DavidGR777/Feed-Tech-Solution/docs/High level schemes/Arquitectura.jpg

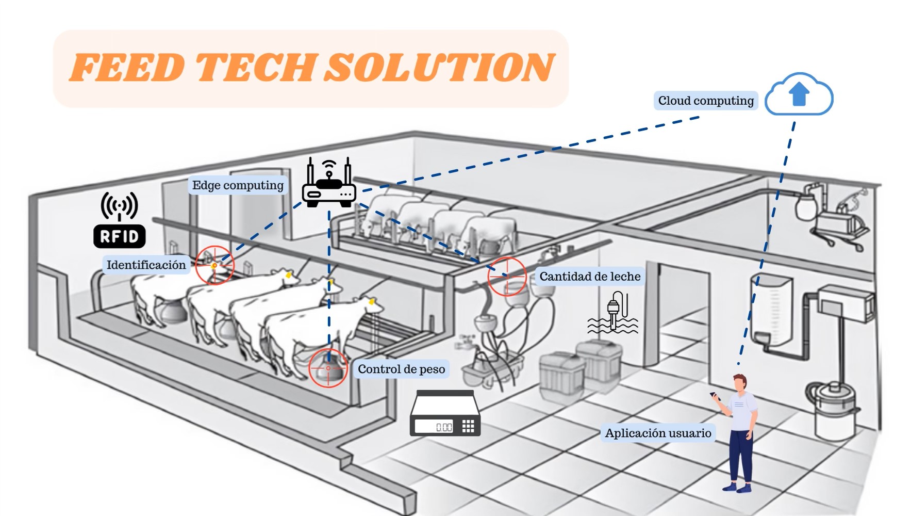
docs/High level schemes/Arquitectura.jpg
