DavidGR777/Feed-Tech-Solution/docs/High level schemes/Diagrama de bloques.png

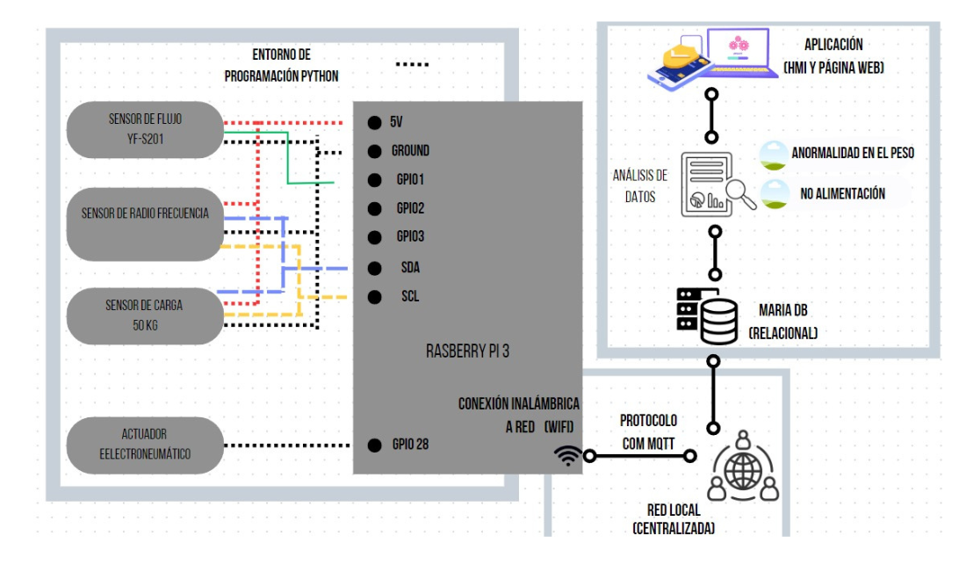
docs/High level schemes/Diagrama de bloques.png
