DavidGR777/Feed-Tech-Solution/docs/images/Folletos.jpg

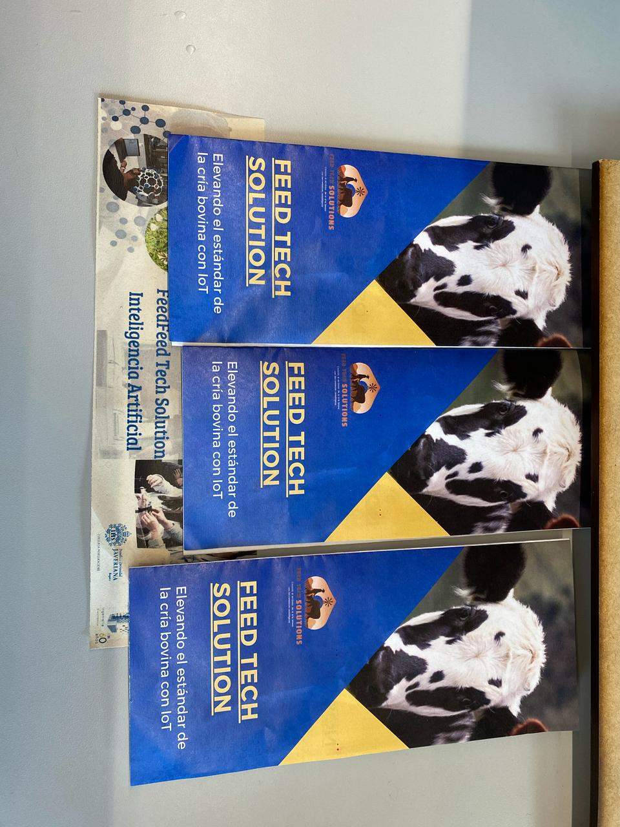
docs/images/Folletos.jpg
