DavidGR777/Feed-Tech-Solution/docs/images/Implementacion 1.jpg

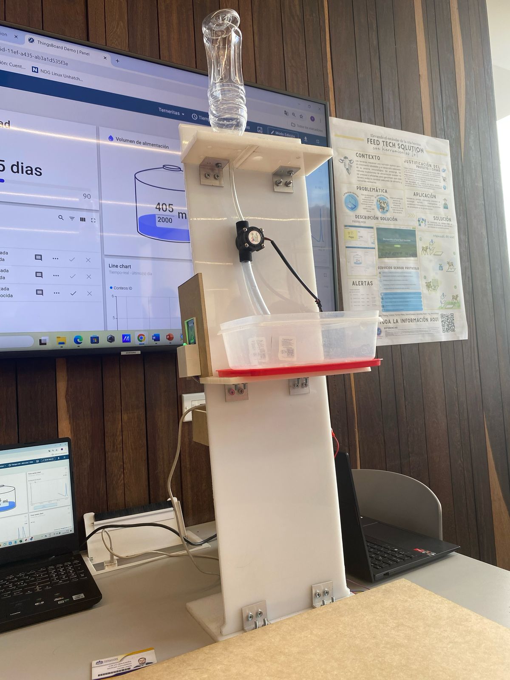
docs/images/Implementacion 1.jpg
