DavidGR777/Feed-Tech-Solution/docs/images/Implementacion 2.jpg

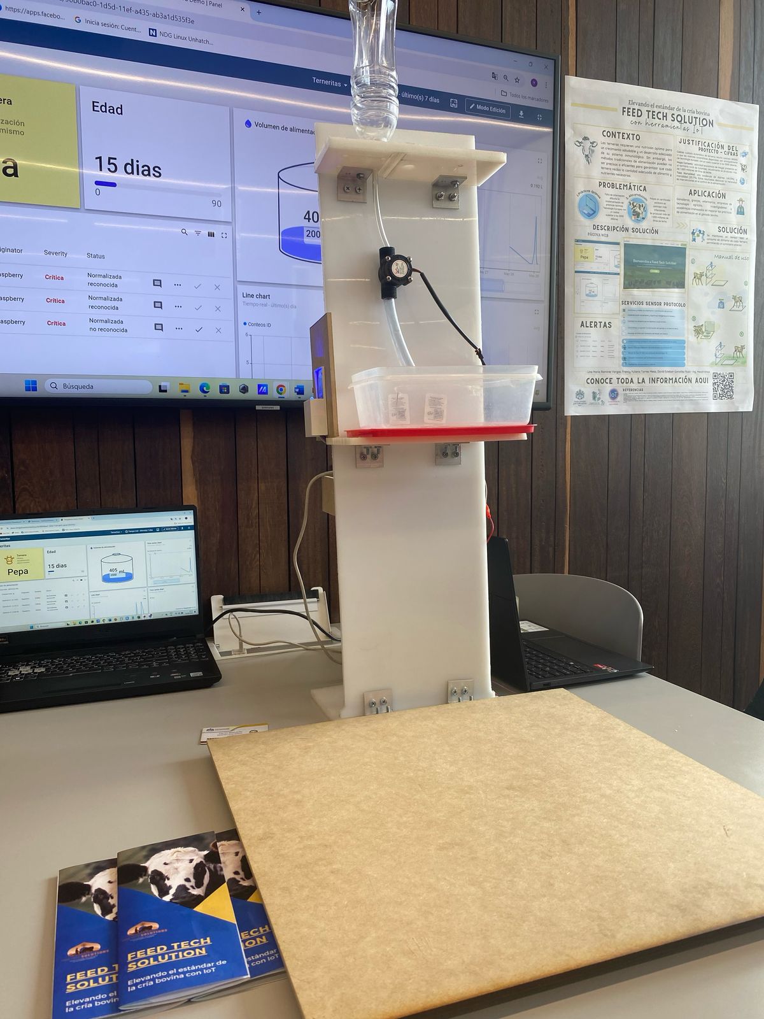
docs/images/Implementacion 2.jpg
