DavidGR777/Feed-Tech-Solution/web-page/img/__page-0001.jpg

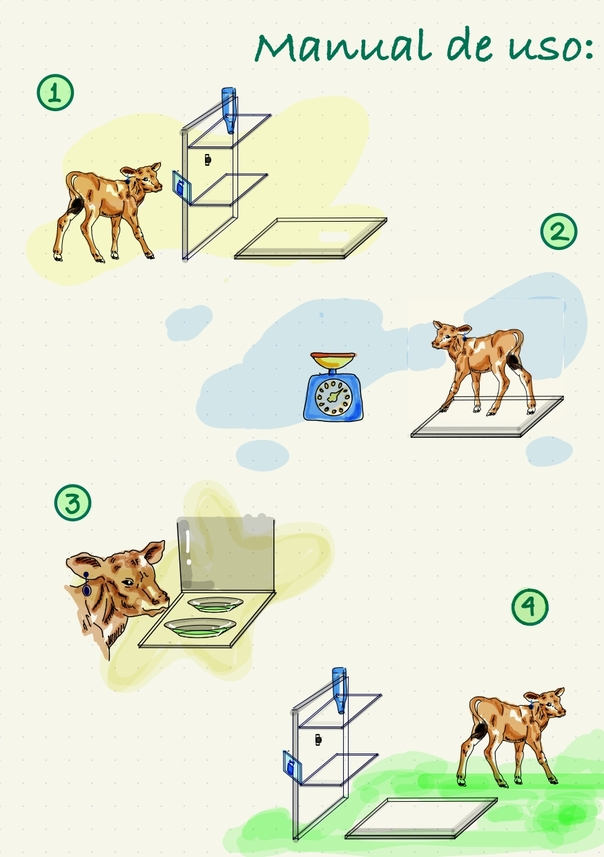
web-page/img/__page-0001.jpg
