DavidGR777/Feed-Tech-Solution/web-page/img/footer.jpg

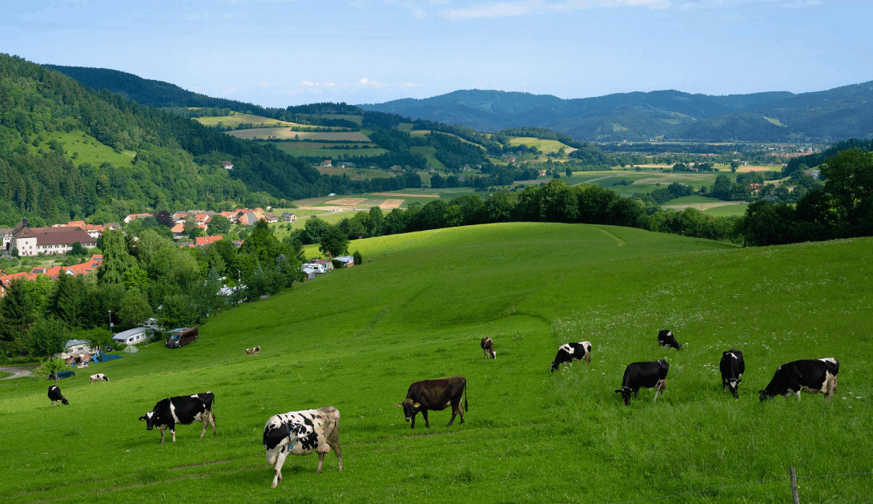
web-page/img/footer.jpg
