DavidGR777/Feed-Tech-Solution/web-page/img/header.jpg

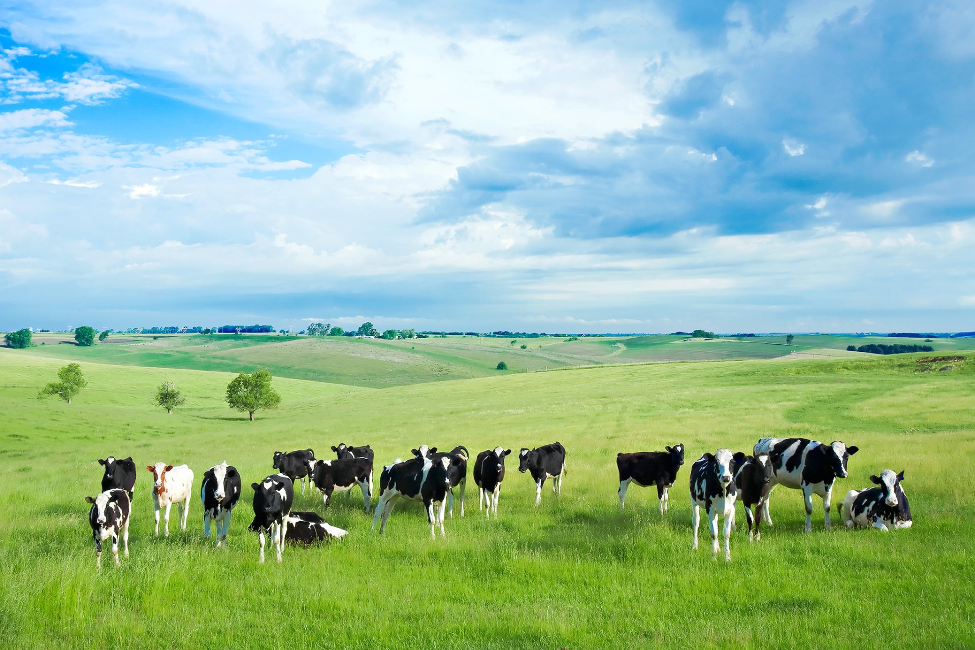
web-page/img/header.jpg
