DavidGR777/Feed-Tech-Solution/web-page/img/imagen1.png

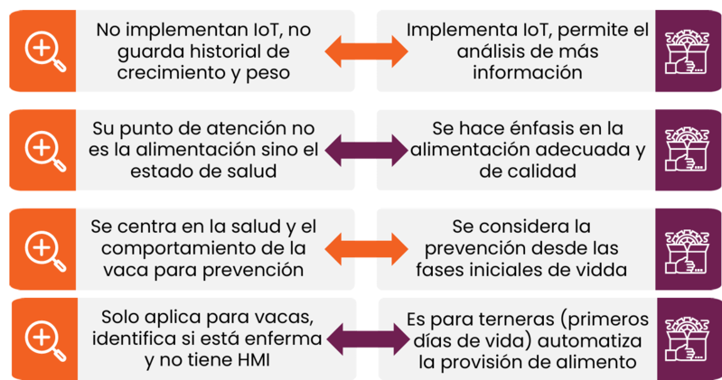
web-page/img/imagen1.png
