DavidGR777/Feed-Tech-Solution/web-page/img/imagen2.png

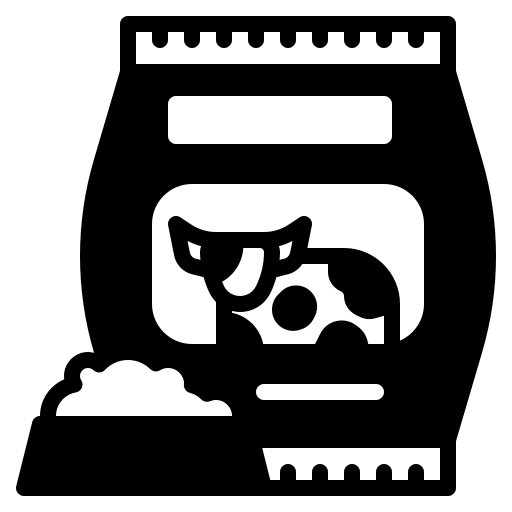
web-page/img/imagen2.png
