DavidGR777/Feed-Tech-Solution/web-page/img/imagen5.jpg

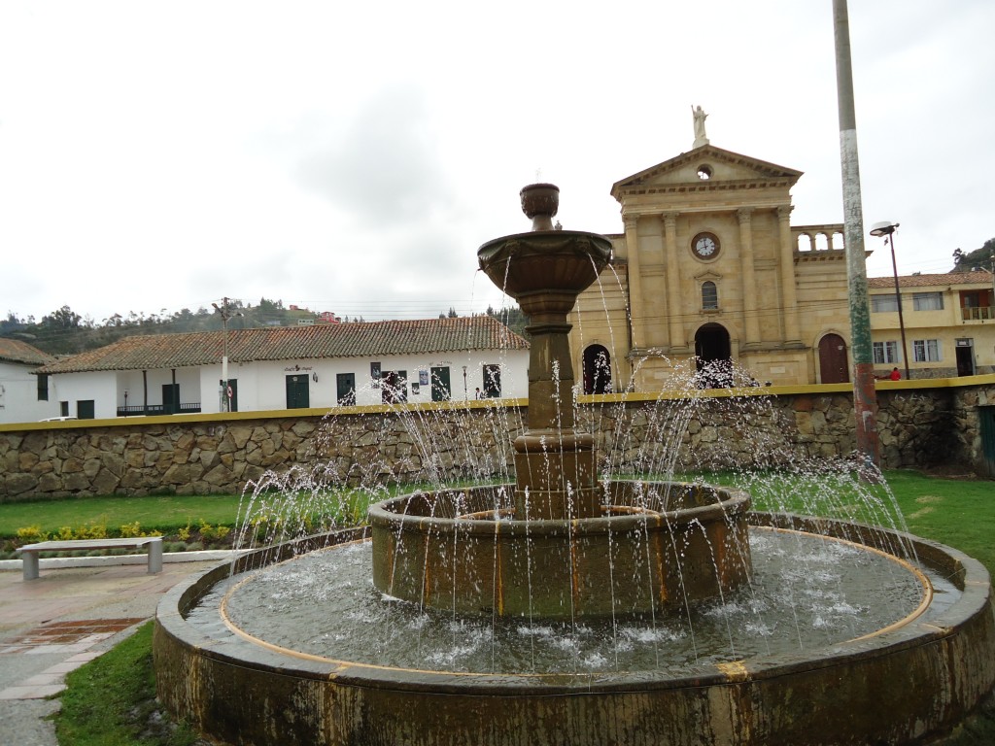
web-page/img/imagen5.jpg
