DavidGR777/Feed-Tech-Solution/web-page/img/imagen6.jpeg

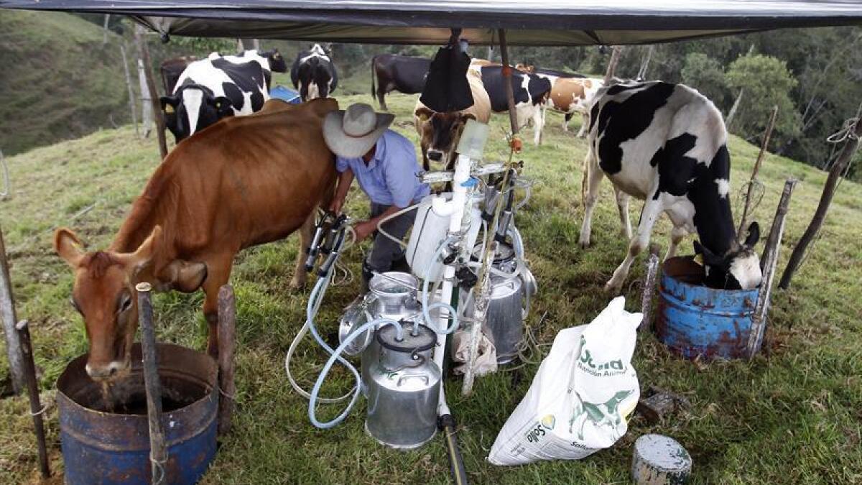
web-page/img/imagen6.jpeg
