DavidGR777/Feed-Tech-Solution/web-page/img/imagen7.jpg

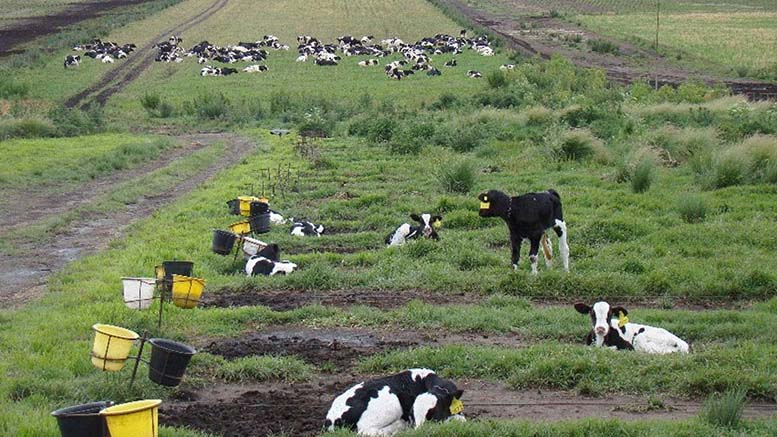
web-page/img/imagen7.jpg
