DavidGR777/Feed-Tech-Solution/web-page/img/imagen8.jpg

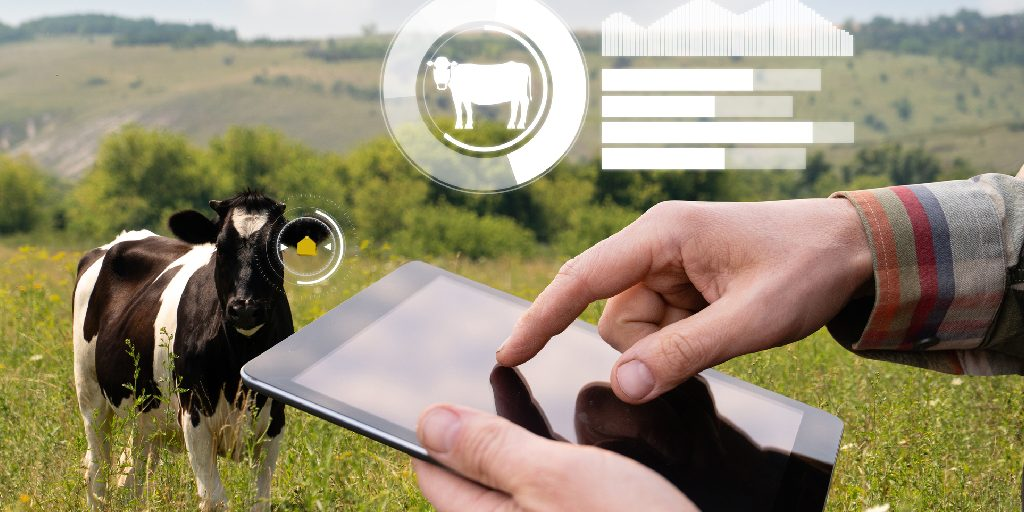
web-page/img/imagen8.jpg
