DavidGR777/Feed-Tech-Solution/web-page/img/imagen10.png

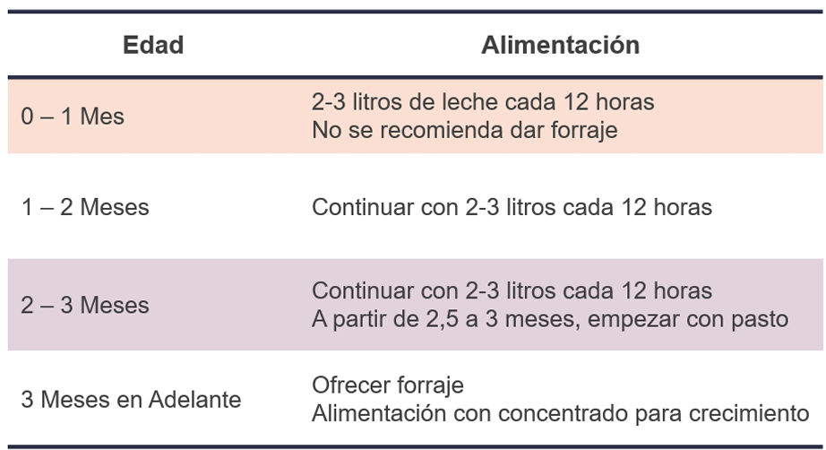
web-page/img/imagen10.png
