DavidGR777/Feed-Tech-Solution/web-page/img/imagen14.png

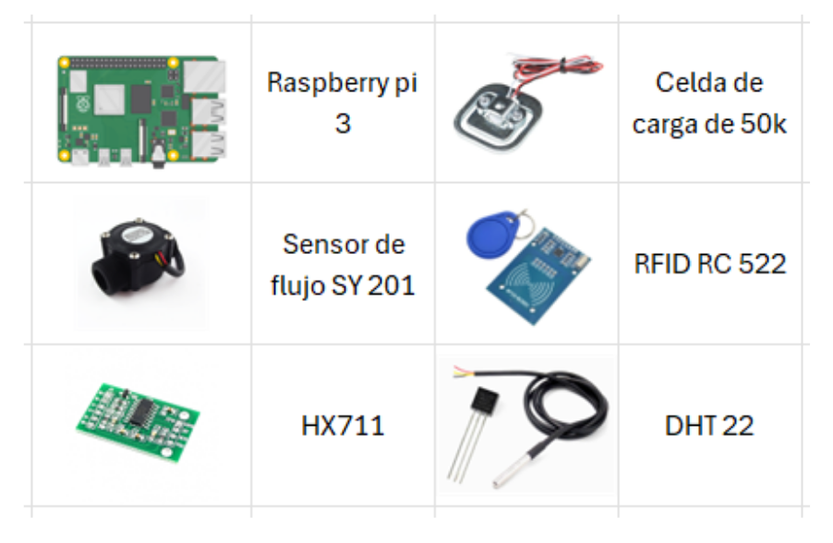
web-page/img/imagen14.png
