DavidGR777/Feed-Tech-Solution/web-page/img/imagen15.jpg

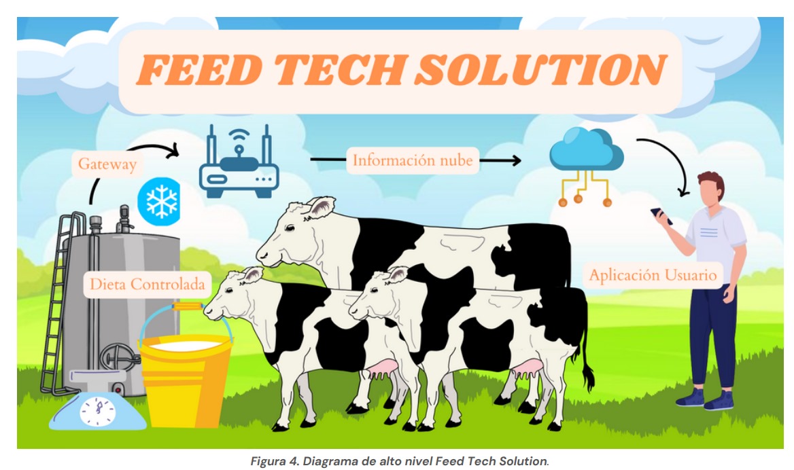
web-page/img/imagen15.jpg
