DavidGR777/Feed-Tech-Solution/web-page/img/imagen16.png

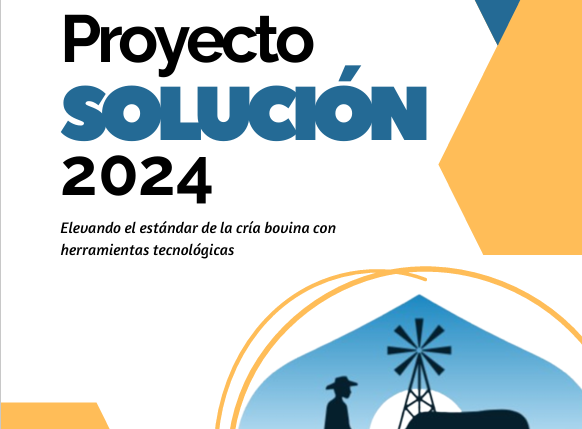
web-page/img/imagen16.png
