DavidGR777/Feed-Tech-Solution/web-page/img/img-2.jpg

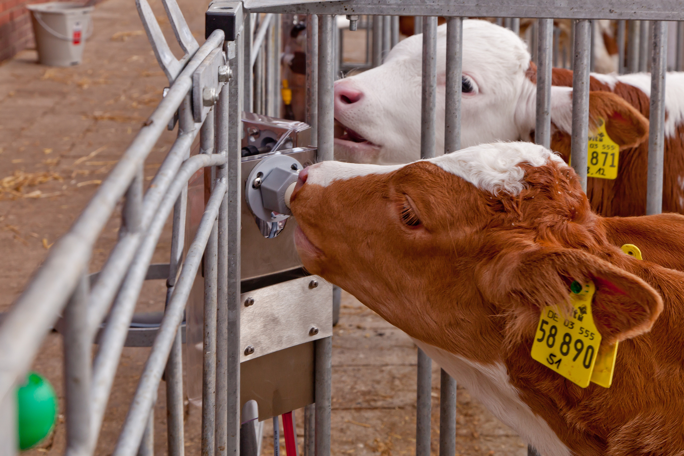
web-page/img/img-2.jpg
