DavidGR777/Feed-Tech-Solution/web-page/img/img-9.jpg

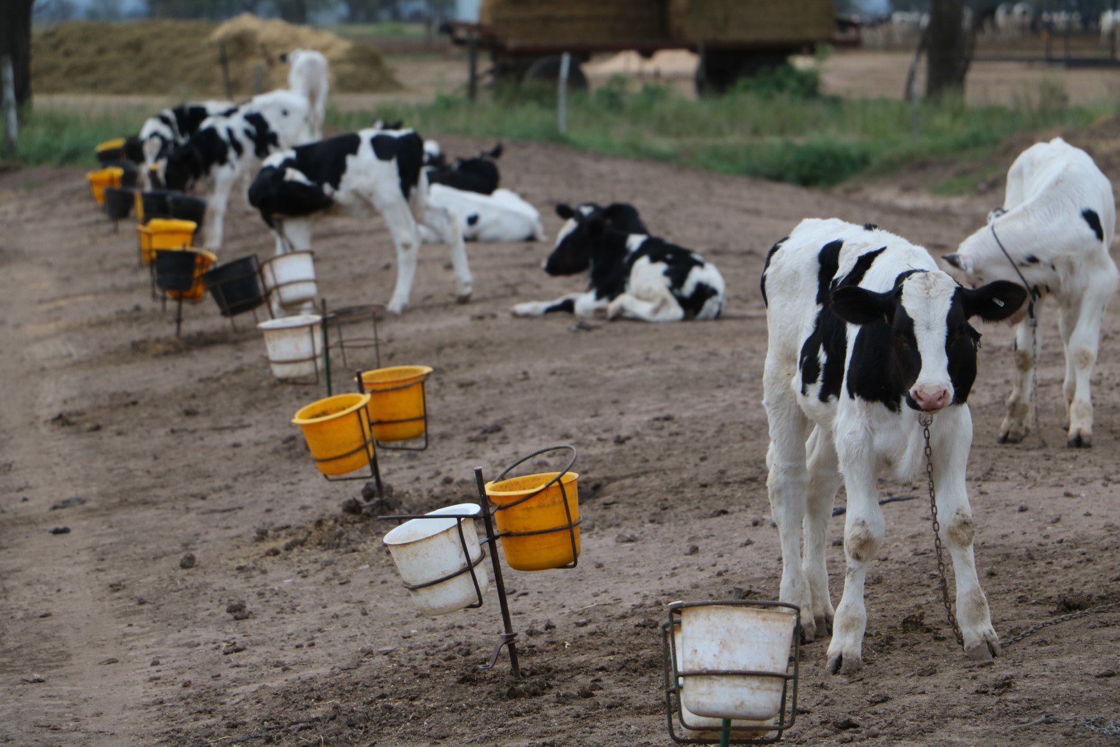
web-page/img/img-9.jpg
