DavidGR777/Feed-Tech-Solution/web-page/img/img-17.jpg

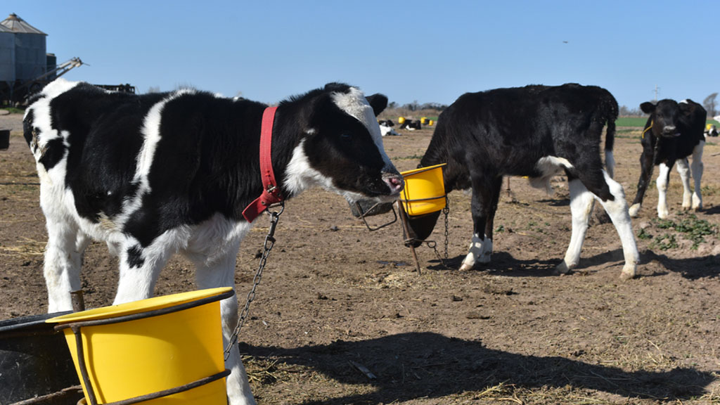
web-page/img/img-17.jpg
