DavidGR777/Feed-Tech-Solution/cad-design/Celda de carga/SIDE RIVET, 50 kg Load Cell Resistance Strain Half Bridge Sensor.SLDPRT

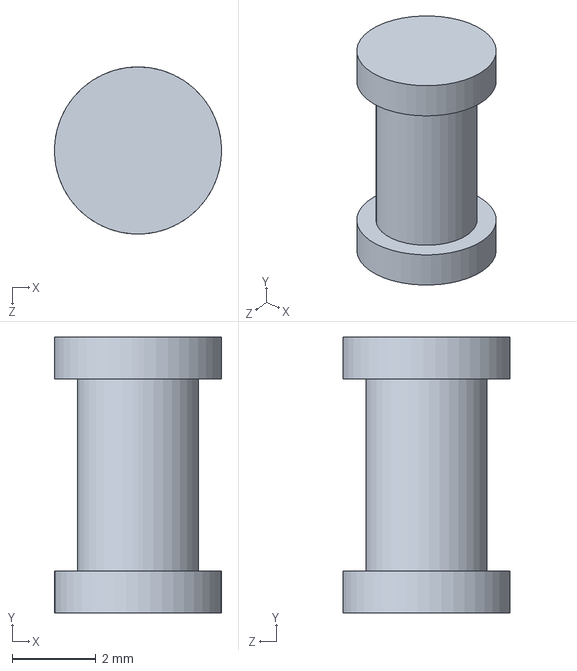
[picture p64: CAD file, 2025-03-24]
cad-design/Celda de carga/SIDE RIVET, 50 kg Load Cell Resistance Strain Half Bridge Sensor.SLDPRT
4.00 x 6.60 x 4.00 mm
