DavidGR777/Feed-Tech-Solution/cad-design/LCD/metal_casing.SLDPRT

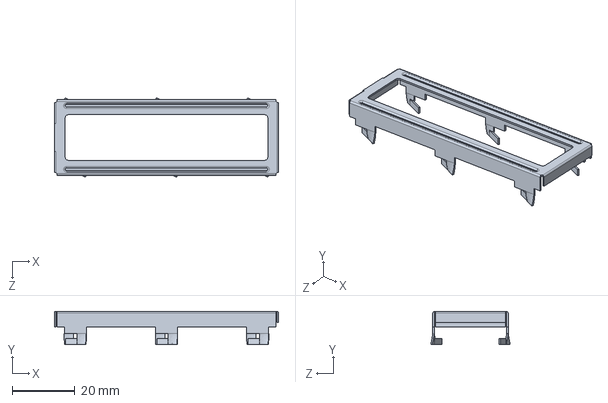
[picture p65: CAD file, 2025-03-24]
cad-design/LCD/metal_casing.SLDPRT
71.2 x 10.6 x 25.3 mm
