DavidGR777/Feed-Tech-Solution/cad-design/Soporte RFID.SLDPRT

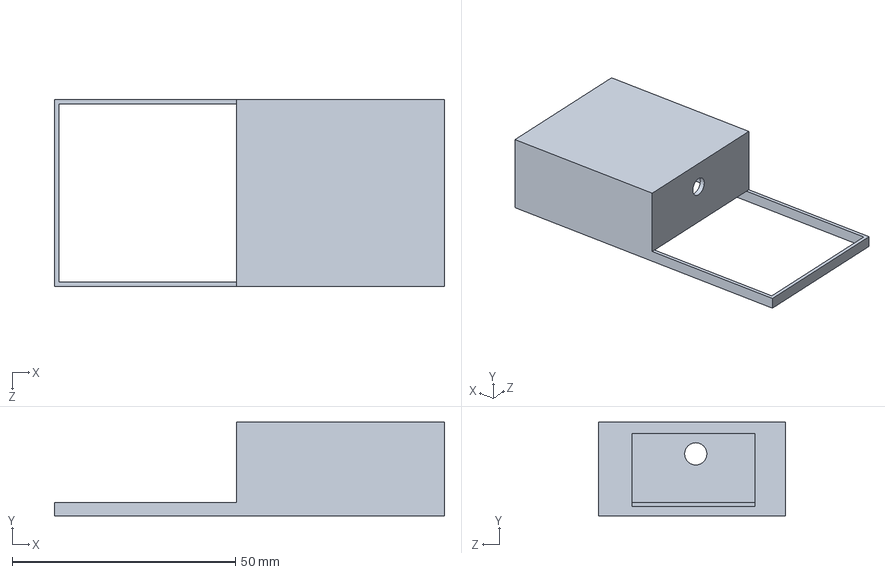
[picture p66: CAD file, 2025-03-24]
cad-design/Soporte RFID.SLDPRT
87.3 x 21.0 x 41.9 mm
