DavidGR777/Feed-Tech-Solution/cad-design/Celda de carga/WIRED CONNECTION, 50 kg Load Cell Resistance Strain Half Bridge Sensor.SLDPRT

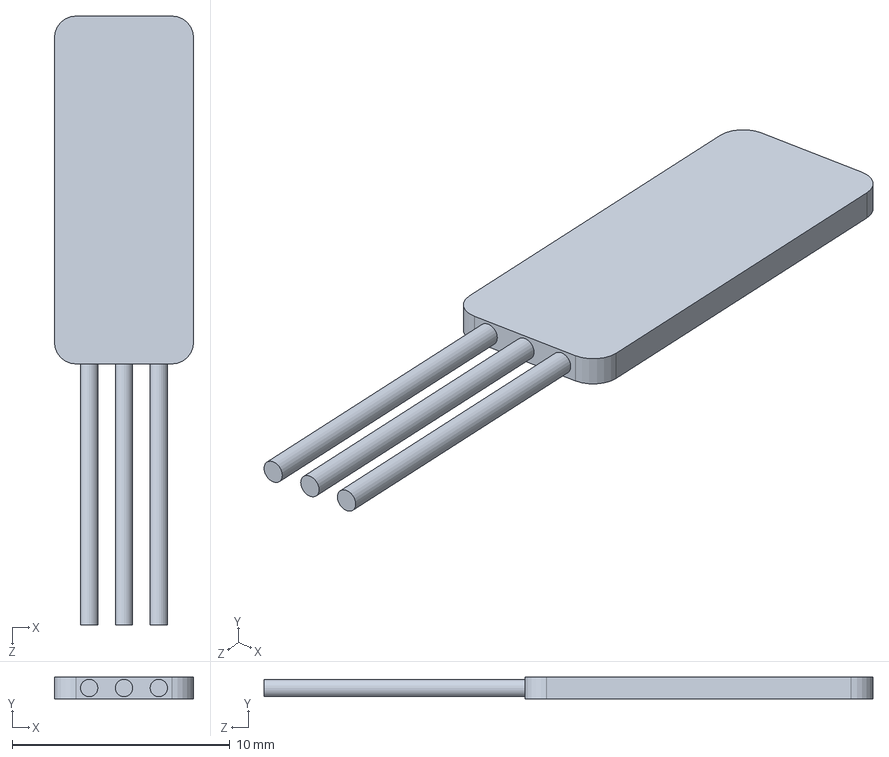
[picture p67: CAD file, 2025-03-24]
cad-design/Celda de carga/WIRED CONNECTION, 50 kg Load Cell Resistance Strain Half Bridge Sensor.SLDPRT
6.40 x 1.00 x 28.0 mm
