DavidGR777/Feed-Tech-Solution/cad-design/LCD/conductors.SLDPRT

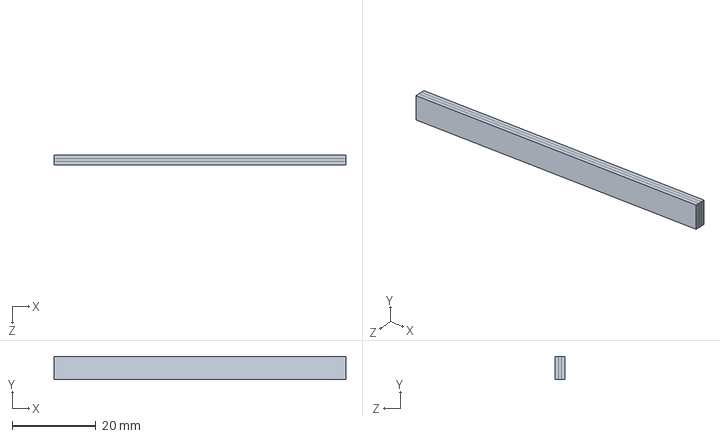
[picture p68: CAD file, 2025-03-24]
cad-design/LCD/conductors.SLDPRT
69.7 x 5.50 x 2.50 mm
