DavidGR777/Feed-Tech-Solution/cad-design/RFID-RC522 simple.SLDPRT

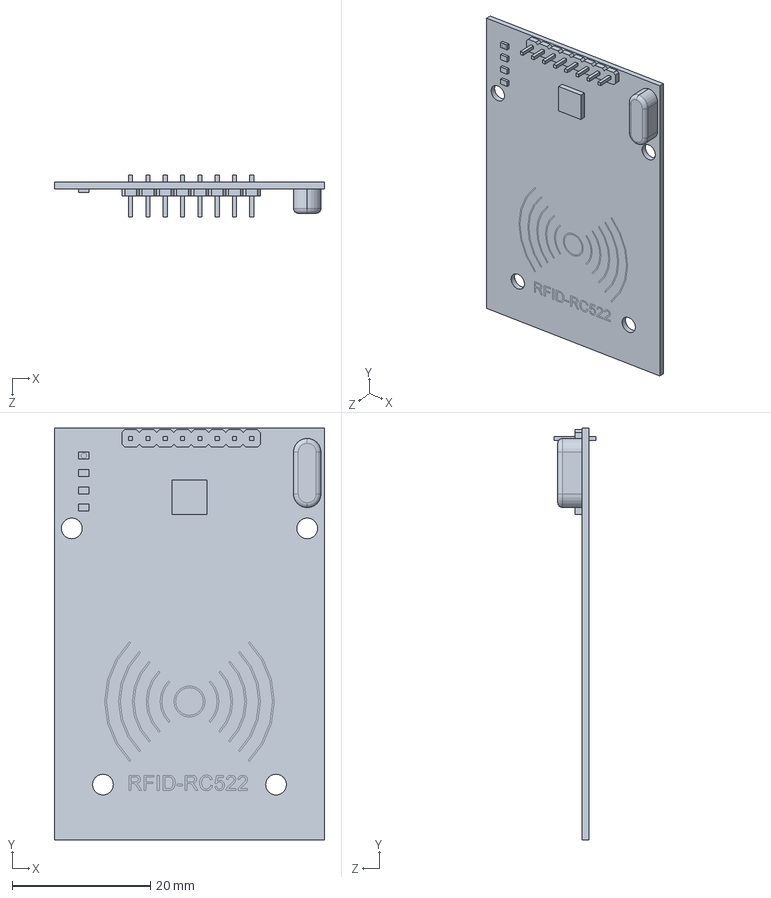
[picture p69: CAD file, 2025-03-24]
cad-design/RFID-RC522 simple.SLDPRT
39.0 x 59.5 x 6.00 mm
